Soulboy420/BP_flappyBird/hardware/redesign/doc/quellen.md

# Herstellerquellen und Pinprüfung

Recherche 05.–06.09.2026. Maßgeblich sind die verlinkten Originalunterlagen, nicht Händler-Kurztexte. „S.“ bezeichnet die im PDF gedruckte Seite, soweit vorhanden; sonst die PDF-Seite. Produktseiten ohne Revision sind mit Abrufdatum dokumentiert. Lokale PDFs unter `quellen/` sind ergänzende Arbeitskopien; deren Fehlen bedeutet nicht, dass eine unten verlinkte Quelle offline mitgeliefert wird. Typische Kurven werden nicht als garantierte Grenzwerte ausgegeben.

## Aktive Bauteile und Architektur

| Bauteil / Quelle | Revision / Fundstelle | Geprüfte Aussage und Umsetzung |
|---|---|---|
| [Espressif ESP32-C3-WROOM-02](https://www.espressif.com/sites/default/files/documentation/esp32-c3-wroom-02_datasheet_en.pdf) | v1.7; Pin Definitions, Strapping Pins, Electrical Characteristics, Module Dimensions | U1.1 Versorgung, .2 EN, .3–.8 GPIO4–9, .9 GND, .10 GPIO10, .11/.12 GPIO20/21, .13/.14 GPIO18/19, .15–.18 GPIO3–0, .19 EP/GND. 3,0…3,6 V, Straps 2/8/9, Modulgeometrie. |
| [ESP32-C3 SoC](https://documentation.espressif.com/esp32-c3_datasheet_en.html) | v2.4; §2.4, §3.1/3.2 | GPIO21 ist ROM-UART-TX; deshalb nur LED an diesem Pin. GPIO2 steuert EN2 invertiert über Q7. GPIO3 ist RTC-Wake-Eingang. |
| [Espressif Hardware Design Guidelines](https://documentation.espressif.com/esp-hardware-design-guidelines/en/latest/esp32c3/index.html) | v1.8; Schematic Checklist / PCB Layout Design | USB-Serienwiderstände, 90-Ω-Ziel und Antennenfreiraum. Tatsächlicher Fertigeraufbau bleibt Freigabepunkt. |
| [TI BQ24074](https://www.ti.com/lit/ds/symlink/bq24074.pdf) | SLUS810N, Okt. 2021; §7, §8.5, §9, Layout/Package | U2: 1 TS, 2/3 BAT, 4 CE, 5 EN2, 6 EN1, 7 PGOOD, 8 VSS, 9 CHG, 10/11 OUT, 12 ILIM, 13 IN, 14 TMR, 15 ITERM, 16 ISET, 17 EP. RGT 3×3 mm, Pitch 0,5 mm, EP 1,6×1,6 mm. KISET 797/890/975; VREG bis 4,23 V; IN absolut 28 V. Eigenständiger Lastpfad verhindert verfälschten Ladeabschluss. TS-Grenzen rechtfertigen keine garantierte 0…45-°C-Freigabe. |
| [Torex XC6220](https://product.torexsemi.com/system/files/series/xc6220.pdf) / [Produktserie](https://product.torexsemi.com/en/series/xc6220) | ETR03041-016b; S.3–6,11, Package Information | **PR/SOT-89-5: 1 CE, 2 GND, 3 NC, 4 VIN, 5 VOUT.** Lokales Symbol explizit umgepinnt. PS-Ruhestrom 8 µA typisch/18 µA max unter Testbedingungen; HS 50/108 µA. 10-µF-Referenzbeschaltung. Kein aus typischem Dropout abgeleiteter garantierter Mindest-Akkustand. |
| [TI TPS22919](https://www.ti.com/lit/ds/symlink/tps22919.pdf) | SLVSEN5B, Mai 2019; Pin Configuration, Electrical Characteristics, QOD | U4 DCK: 1 IN, 2 GND, 3 ON, 4 NC, 5 QOD, 6 OUT. OLED und U5 gemeinsam abschaltbar. Ausschaltstrom bis 800 nA über spezifizierten Temperaturbereich. |
| [Nexperia 74LVC125A](https://assets.nexperia.com/documents/data-sheet/74LVC125A.pdf) / [Bestellcodes](https://www.nexperia.com/products/analog-logic-ics/logic/buffers-inverters-transceivers/buffers/serie/74lvc125a/) | Rev.12, 02.05.2025; S.3 Pinning, S.4–6 Limits/Characteristics, Package SOT108-1 | U5 **74LVC125AD,118**, SO14: OE 1/4/10/13, A 2/5/9/12, Y 3/6/8/11, GND 7, VCC 14. IOFF ausdrücklich für ausgeschaltete Versorgung spezifiziert; max. 10 µA je Pin bis 85 °C. Vier 220-Ω-Serienwiderstände begrenzen Kurzschlussstrom. Kein ungeprüfter Herstellerersatz. |
| [TI TPD2E2U06](https://www.ti.com/lit/ds/symlink/tpd2e2u06.pdf) | Rev.C; Pin Configuration / Electrical Characteristics / DCK | D2…D9, **SC70-3: 1 IO1, 2 IO2, 3 GND**, kein VCC-Pin. 5,5-V-Standoff, geringe Kapazität. Die angegebenen ESD-Pegel gelten für das Bauteil unter dessen Prüfbedingungen. |
| [Diodes DMP2035U](https://www.diodes.com/datasheet/download/DMP2035U.pdf) | DS31830 Rev.11-2, Juni 2025; S.1–3 | Q1 SOT23: 1 G, 2 S, 3 D. 20 V VDS, ±10 V VGS, max. 45 mΩ bei −2,5 V. Source am BQ-BAT-Knoten, Drain am Pack. |
| [Diodes BSS84](https://www.diodes.com/datasheet/download/BSS84.pdf) | DS30149 Rev.27-2, Mai 2026; S.1–3 | Q2/Q4: 1 G, 2 S, 3 D. P-Kanal, 50 V VDS, ±20 V VGS. Einsatz als Detektor bzw. Kleinstrom-Messzweig, nicht als Hauptleistungs-FET. |
| [Diodes 2N7002](https://www.diodes.com/datasheet/download/2N7002.pdf) | Datenblatt am 05.09.2026; S.1–3 / Pin Assignment, Electrical Characteristics | Q3/Q5/Q7: 1 G, 2 S, 3 D. Nur kleine Pullup-/Gate-Ströme. Kein aus dem Namen abgeleiteter 3,3-V-Leistungsbetrieb. |
| [Diodes DMN2056U](https://www.diodes.com/datasheet/download/DMN2056U.pdf) | DS38480 Rev.2-2, Juli 2021; S.1–3 | Q6: 1 G, 2 S, 3 D; bei 2,5 V spezifizierter Logic-Level-FET; 45 mΩ max., VDS 20 V, VGS ±8 V. Piezo über MOSFET statt direkt am GPIO. |
| [Diodes BAV19W–BAV21W](https://www.diodes.com/datasheet/download/BAV19W-BAV21W.pdf) / [BAV19W](https://www.diodes.com/part/view/BAV19W) | Datenblatt am 05.09.2026; Pin Assignment / Package / Characteristics | D12 BAV19W-7-F, SOD123. Band = Kathode = PCB-Pad 1 an PIEZO_P; Pad 2 Anode an PIEZO_N. Rückschlagklemme für kapazitive Last. |
| [ADI AN-171](https://www.analog.com/en/resources/app-notes/an-171.html) | Reverse Voltage Protection for Battery Chargers, insbesondere Abb.7 | Zwei-PMOS-Verpolerkennung; mögliche Verriegelung beim Akkuwechsel mit bereits aktivem Ladeeingang. R6 bleibt DNP, Akku-vor-USB als dokumentierte Einschränkung. Keine ungemessene Hot-Swap-Garantie. |

## Passive Bauteile, Schutz und Mechanik

| Bauteil / Quelle | Fundstelle | Prüfung / Entscheidung |
|---|---|---|
| [Littelfuse 466 Sicherung](https://www.littelfuse.com/assetdocs/fuse-466-datasheet?assetguid=dbe9bcd7-6072-4adf-bf5b-d33e52a6b90f) | GD 06/21/23; S.1 Electrical Characteristics, S.2 Derating, S.3 Dimensions/Ordering | **0466001.NRHF**, 1 A, 1206, 63 V. 3,175×1,524 mm; symmetrische Pads 1/2. 75 mΩ typ., 2× Nennstrom: max.5 s; 3×: max.0,2 s. Nicht mit der kleineren 467-Familie verwechseln. |
| [Littelfuse SMBJ](https://www.littelfuse.com/~/media/electronics/datasheets/tvs_diodes/littelfuse_tvs_diode_smbj_datasheet.pdf.pdf) | 2020-Fassung; Electrical Characteristics, Case Dimensions, Polarity | SMBJ6.0A unidirektional, SMB. 6,0-V-Standoff, 10,3 V Klemmung bei 58,3 A im spezifizierten Puls. Kathodenband an VBUS/Pad 1. Der neuere indizierte Herstellerlink lieferte beim Direktabruf 404; kein behaupteter Vergleich einer nicht lesbaren neuen PDF-Fassung. |
| [TDK 22 µF / 16 V](https://product.tdk.com/en/search/capacitor/ceramic/mlcc/info?part_no=C3216X5R1C226M160AB) / [Charakterisierungsblatt](https://product.tdk.com/en/system/files/dam/doc/product/capacitor/ceramic/mlcc/charasheet/c3216x5r1c226m160ab.pdf) | Produktseite „Production“, Abruf 05.09.2026; Charakterisierungsblatt 03.01.2016, 1 Seite | C3…C11: 1206, 3,2×1,6 mm, 1,6 mm Höhe, ±20 %, X5R, IR ≥4 MΩ. DC-Bias-Kurve vorhanden; Bildabruf nicht erfolgreich, deshalb keine erfundene Kurvenablesung. Kapazitätsfreigabe explizit offen. |
| [TDK 100 nF](https://product.tdk.com/en/search/capacitor/ceramic/mlcc/info?part_no=C2012X7R1H104K085AA) | Produktseite, Abruf 05.09.2026 | C2012X7R1H104K085AA, 0805, 50 V, X7R. Nichtpolar, Pads 1/2 austauschbar. |
| [TDK 1 µF](https://product.tdk.com/en/search/capacitor/ceramic/mlcc/info?part_no=C2012X7R1E105K125AB) | Produktseite, Abruf 05.09.2026 | C2012X7R1E105K125AB, 0805, 25 V, X7R, ±10 %. |
| [KEMET 18 pF](https://search.kemet.com/download/specsheet/C0805C180J5GACTU) | S.1, Abruf 05.09.2026 | C17/C18 DNP: C0805C180J5GACTU, 0805, 50 V, C0G, ±5 %. |
| [Panasonic Null-Ohm](https://industrial.panasonic.com/ww/products/pt/general-purpose-chip-resistors/models/ERJ6GEY0R00V) / [ERJ6ENF-Familienbeispiel](https://industrial.panasonic.com/jp/products/pt/general-purpose-chip-resistors/models/ERJ6ENF28R0V) | Produktdaten / Dimensions / Rating, Abruf 05.09.2026 | ERJ-6GEY0R00V für 0 Ω; ERJ-6ENF-Wertcodes gemäß BOM für 1 %, 0805, 0,125 W. Unpolar. R36 nahe seiner Belastungsgrenze bei Dauerkurzschluss; Temperatur-Derating beachten. |
| [GCT USB4105 Zeichnung](https://gct.co/files/drawings/usb4105.pdf) / [Spezifikation](https://gct.co/files/specs/usb4105-spec.pdf) | Zeichnung Pin Assignment; Spec Rev.A3, 27.02.2023 | USB4105-GF-A. A1/B12 etc. Masse, A4/B9 etc. VBUS, A5 CC1/B5 CC2, A6/B6 D+, A7/B7 D−, SBU NC. Doppelte Signalkontakte verbunden; mechanische Schirmanschlüsse auf GND. |
| [JST PH](https://www.jst-mfg.com/product/pdf/eng/ePH.pdf) | PCB Layout / Header / Ordering, Abruf 05.09.2026 | B2B-PH-K-S(LF)(SN), 2,00-mm-Raster. Physische Pin-1-Ansicht geprüft; die Zuordnung zu Akku+ bzw. NTC legt dieser Entwurf fest. Ein PH-Gehäuse garantiert keine fremde Kabelpolung. |
| [JST XH](https://www.jst-mfg.com/product/pdf/eng/eXH.pdf) | S.2 Leiterplattenansicht, S.5 Top Entry Header, Abruf 06.09.2026 | B8B-XH-A(LF)(SN): 2,50-mm-Raster, Pinspanne 17,5 mm, Körperbreite 22,4 mm. B2B-XH-A für J4/J5. Pad1 ist markiert; 1:1-Abgleich mit Gegensteckern bleibt nötig. |
| [C&K OS Series](https://www.littelfuse.com/assetdocs/littelfuse-ck-slide-os-series-datasheet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) | CM 06/16/25; S.1 Kontaktmaterial, S.3 OS102 | OS102011MS2QN1: SPDT, Pin2 gemeinsam, 1–2/2–3, nicht kurzschließend; drei elektrische und zwei Befestigungsbohrungen. Keine bestätigte Mindestlast für wenige µA; Schaltzuverlässigkeit am Prototyp prüfen. |
| [Semitec AT](https://www.semitec-global.com/uploads/2022/01/NTC_thermistors_Circuit_129M.pdf) / [Serie](https://www.semitec-global.com/products/thermistor_at/) | 103AT-2-Zeile, R/T und Thermal Time Constant | Externes NTC-Teil 10 kΩ ±1 %, B=3435 K ±1 %, ca.15 s thermische Zeitkonstante. Nicht polar; thermische Befestigung am Pack ist Teil der Qualifikation. |
| [Kingbright APT2012EC](https://www.kingbrightusa.com/images/catalog/spec/apt2012ec.pdf) / [APT2012SGC](https://www.kingbrightusa.com/images/catalog/spec/apt2012sgc.pdf) | EC Ver.13A 2021 / SGC 2025; Package Dimensions / Polarity / Electrical | D10 rot, D11 grün, 0805. Kathode Pad1, Anode Pad2. Serienwiderstand 3,3 kΩ; Lichtstärke bei kleinem Strom messen. |

## Leiterbahn-Vorabschätzung

[TI SNVA766, April 2017, S.16, Gleichung 3](https://www.ti.com.cn/cn/lit/pdf/snva766) dokumentiert die verwendete IPC-2221-Näherung für Außenlagen. Sie liefert eine rechnerische Eigenerwärmung, keine validierte Gehäusetemperatur. Die Annahmen und aus dem PCB ausgelesenen VBAT-Leiterlängen stehen in `designentscheidungen.md`.

## Quellen zum Ausgangsentwurf

- [Microchip MCP73831/2, DS20001984G](https://ww1.microchip.com/downloads/en/DeviceDoc/20001984g.pdf), Charge Termination / Typical Application: Systemlast am BAT-Knoten beeinflusst den Abschluss.
- [Microchip AN1149](https://ww1.microchip.com/downloads/en/Appnotes/01149c.pdf), Load Sharing: zusätzlicher Systempfad erforderlich, wenn Laden und Last unabhängig behandelt werden sollen.
- [Diodes AP2112, DS39724 Rev.2-2, Juni 2017](https://www.diodes.com/datasheet/download/AP2112.pdf), S.8: Ruhestrom typ.55/max.80 µA, Ausschaltstrom typ.0,01/max.1 µA. Kein 5-µA-Gesamtbudget mit dauerhaft aktivem Regler.

## Reichweite des Pin-Nachweises

`output/pinmapping.csv` listet jedes physische nummerierte Pad mit Herstellerteilenummer, Symbolpin und tatsächlichem Netz. `verification/consistency.json` gleicht diese Zuordnung unabhängig zwischen nativer XML-Netzliste und gespeichertem PCB ab. Identische Mehrfachpads (USB-Schirm, EP) müssen dasselbe Netz führen. NC-Pins sind ausdrücklich unverbunden; Bohrungen besitzen keine elektrischen Pins. Unpolare R/C/Sicherungen sind symmetrisch. LEDs, Dioden, FETs und ICs wurden anhand der oben genannten Pin-/Gehäusezeichnungen geprüft. Für freie Testpads ist keine Keystone-Montage vorgesehen; der BOM-Hinweis ist kein Bestückungsauftrag.

Die lokalen KiCad-Footprints enthalten die verbindlichen Lötflächen. U2 nutzt einen geometrisch passenden generischen WQFN-3D-Körper; U3 einen vereinfachten SOT-89-5-Hüllkörper. Diese beiden Visualisierungsmodelle ersetzen keine Herstellerzeichnung und sind keine mechanische Freigabe.
