Soulboy420/BP_flappyBird/hardware/redesign/output/platine-3d.png

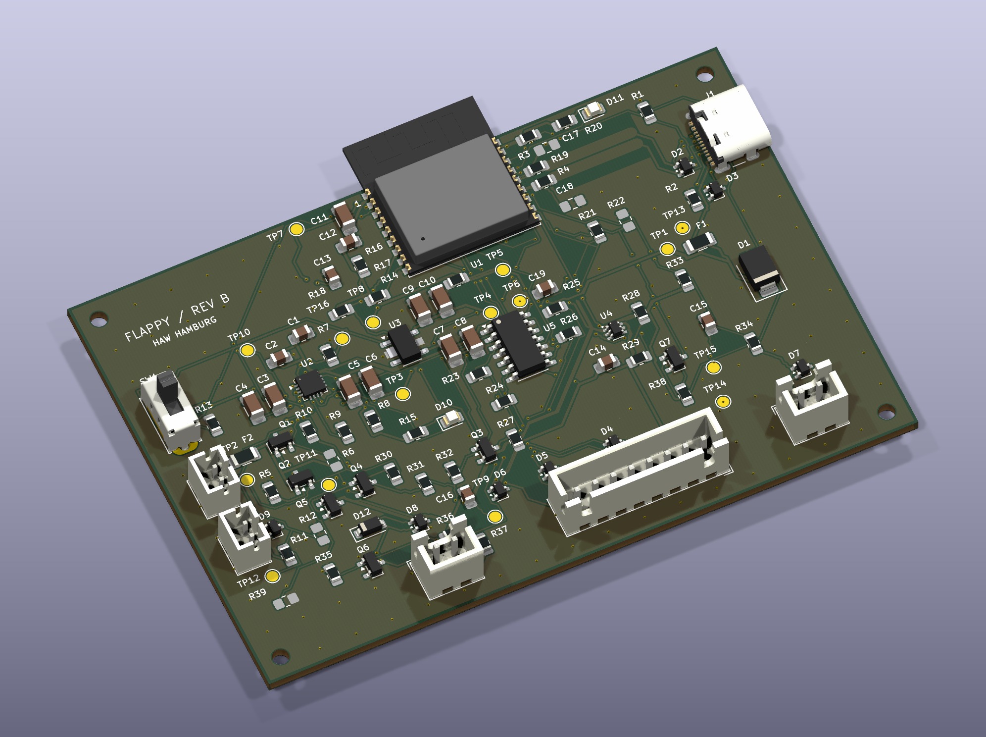
hardware/redesign/output/platine-3d.png
