Soulboy420/BP_flappyBird/hardware/redesign/verification/pdf-render/schaltplan-5.png

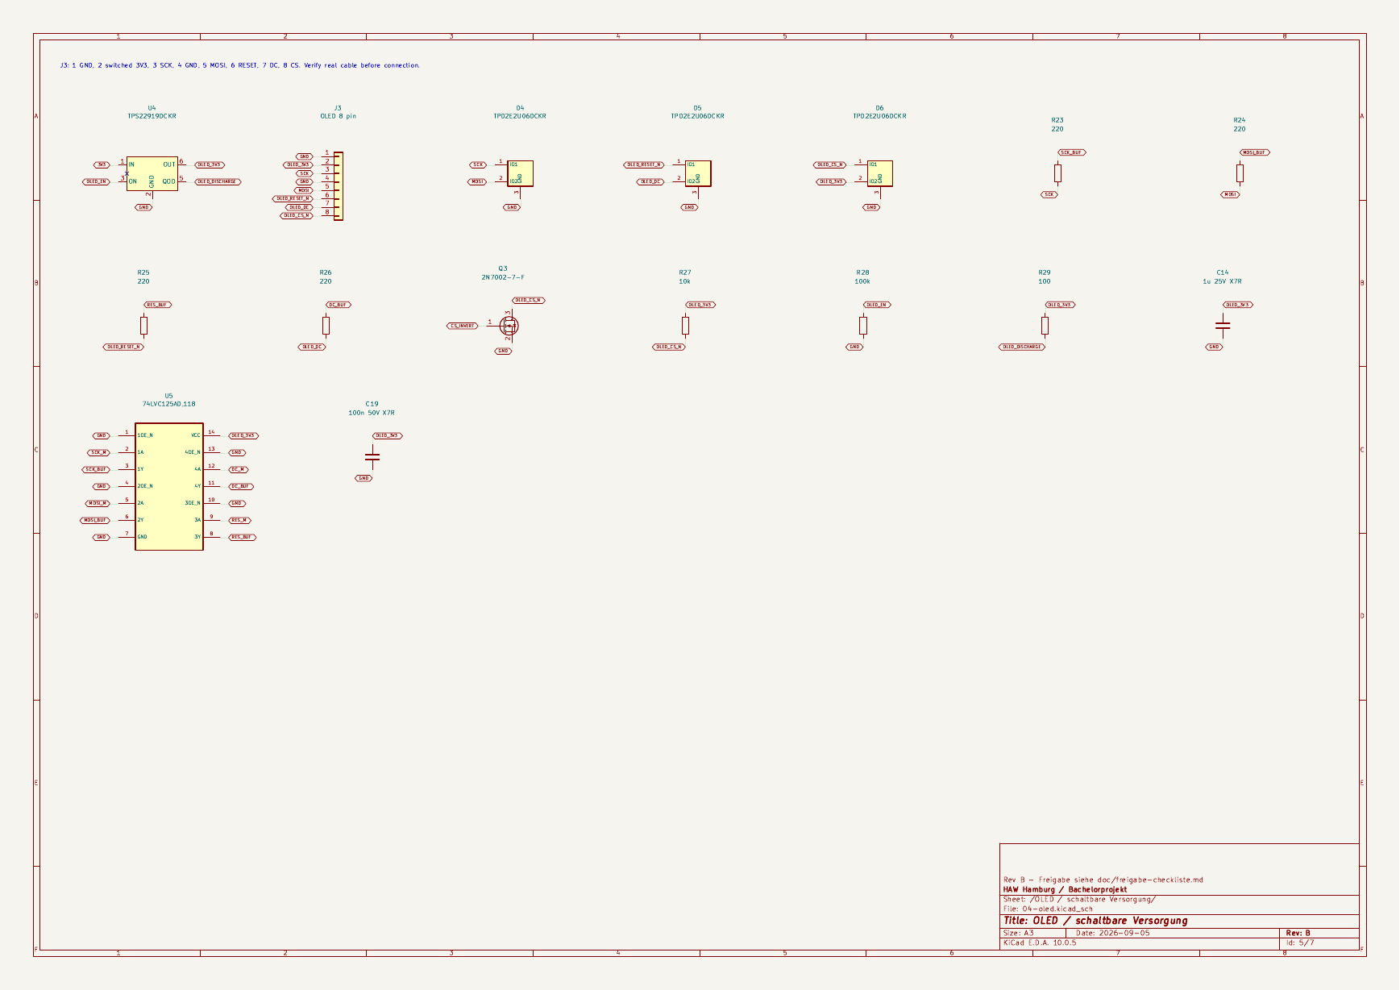
hardware/redesign/verification/pdf-render/schaltplan-5.png
