Soulboy420/BP_flappyBird/hardware/redesign/verification/pdf-render/schaltplan-6.png

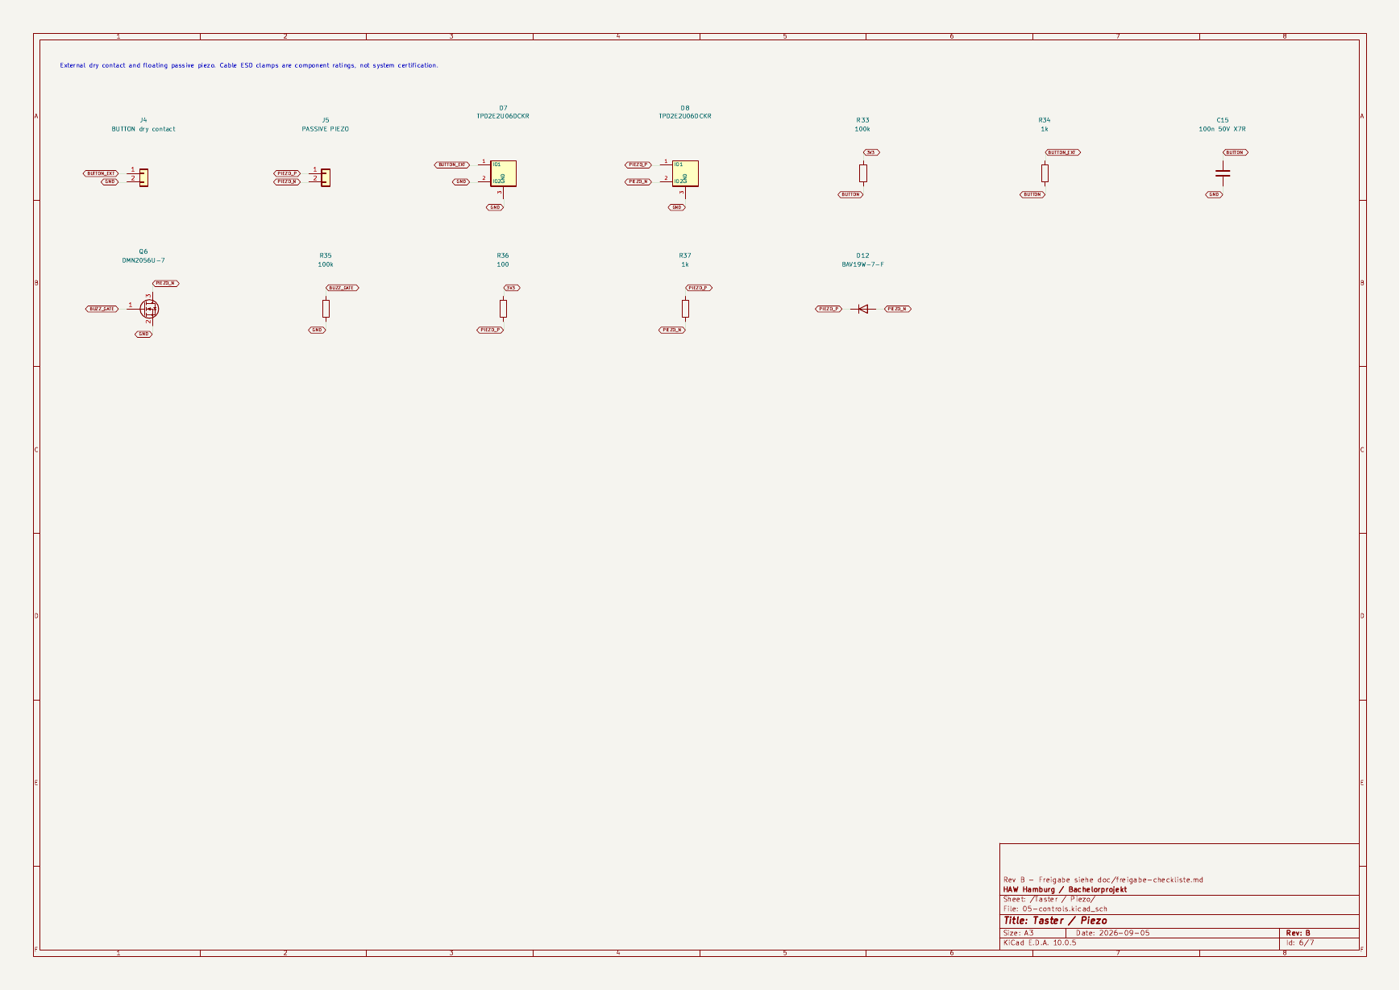
hardware/redesign/verification/pdf-render/schaltplan-6.png
