Soulboy420/BP_flappyBird/hardware/gen/routes.py

# -*- coding: utf-8 -*-
"""Automatisch erzeugt von autoroute.py - nicht von Hand aendern."""
TRACKS = [('GND', 'F.Cu', 0.4, (22.65, 20.0), (22.6, 20.0)), ('GND', 'F.Cu', 0.4, (22.6, 20.0), (21.0, 20.0)), ('GND', 'F.Cu', 0.4, (42.65, 10.0), (42.6, 10.0)), ('GND', 'F.Cu', 0.4, (42.6, 10.0), (41.0, 10.0)), ('GND', 'F.Cu', 0.4, (73.15, 51.5), (73.2, 51.5)), ('GND', 'F.Cu', 0.4, (73.2, 51.5), (73.2, 51.6)), ('GND', 'F.Cu', 0.4, (73.2, 51.6), (71.6, 51.6)), ('VBAT', 'F.Cu', 0.5, (42.6, 11.0), (44.6, 13.0)), ('VBAT', 'F.Cu', 0.5, (44.6, 13.0), (52.0, 13.0)), ('VBAT', 'F.Cu', 0.5, (52.0, 13.0), (56.0, 13.0)), ('VBAT', 'F.Cu', 0.5, (56.0, 13.0), (56.8, 13.8)), ('VBAT', 'F.Cu', 0.5, (56.8, 13.8), (57.4, 13.8)), ('VBAT', 'F.Cu', 0.5, (57.4, 13.8), (57.6, 14.0)), ('VBAT', 'F.Cu', 0.5, (57.6, 14.0), (62.0, 14.0)), ('VBAT', 'F.Cu', 0.5, (62.0, 14.0), (66.4, 14.0)), ('VBAT', 'F.Cu', 0.5, (66.4, 14.0), (69.0, 11.4)), ('VBAT', 'F.Cu', 0.5, (69.0, 11.4), (69.0, 8.0)), ('VBAT', 'F.Cu', 0.5, (66.6, 13.8), (72.8, 20.0)), ('VBAT', 'F.Cu', 0.5, (72.8, 20.0), (73.4, 20.0)), ('VBAT', 'F.Cu', 0.5, (73.4, 20.0), (74.0, 20.6)), ('VBAT', 'F.Cu', 0.5, (74.0, 20.6), (74.0, 22.0)), ('VBAT', 'F.Cu', 0.5, (74.0, 22.0), (73.4, 22.6)), ('VBAT', 'F.Cu', 0.5, (73.4, 22.6), (73.4, 24.0)), ('VBAT', 'F.Cu', 0.5, (73.4, 24.0), (73.2, 24.2)), ('VBAT', 'F.Cu', 0.5, (73.2, 24.2), (73.2, 50.6)), ('VBAT', 'F.Cu', 0.5, (73.2, 50.4), (71.6, 50.4)), ('VBAT', 'F.Cu', 0.5, (71.6, 50.4), (71.4, 50.6)), ('VBAT', 'F.Cu', 0.5, (71.4, 50.6), (71.0, 50.6)), ('VBAT', 'F.Cu', 0.5, (71.0, 50.6), (69.0, 52.6)), ('VBAT', 'F.Cu', 0.5, (69.0, 52.6), (69.0, 57.6)), ('VBAT', 'F.Cu', 0.5, (44.6, 13.0), (42.4, 15.2)), ('VBAT', 'F.Cu', 0.5, (42.4, 15.2), (42.4, 16.4)), ('VBAT', 'F.Cu', 0.5, (42.4, 16.4), (35.0, 23.8)), ('VBAT', 'F.Cu', 0.5, (35.0, 23.8), (35.0, 33.0)), ('BATT_P', 'F.Cu', 0.6, (67.0, 8.0), (67.6, 7.4)), ('BATT_P', 'F.Cu', 0.6, (67.6, 7.4), (67.6, 6.6)), ('BATT_P', 'F.Cu', 0.6, (67.6, 6.6), (70.4, 6.6)), ('BATT_P', 'F.Cu', 0.6, (70.4, 6.6), (71.8, 8.0)), ('BATT_P', 'F.Cu', 0.6, (71.8, 8.0), (76.0, 8.0)), ('USB_DM_CON', 'F.Cu', 0.3, (13.6, 13.0), (14.8, 14.2)), ('USB_DM_CON', 'F.Cu', 0.3, (14.8, 14.2), (15.0, 14.2)), ('USB_DM_CON', 'F.Cu', 0.3, (15.0, 14.2), (17.8, 17.0)), ('USB_DM_CON', 'F.Cu', 0.3, (17.8, 17.0), (17.8, 17.8)), ('USB_DM_CON', 'F.Cu', 0.3, (17.8, 17.8), (19.0, 19.0)), ('USB_DM_CON', 'F.Cu', 0.3, (19.0, 19.0), (22.6, 19.0)), ('VBUS', 'F.Cu', 0.4, (13.6, 8.0), (14.6, 7.0)), ('VBUS', 'F.Cu', 0.4, (14.6, 7.0), (32.0, 7.0)), ('VBUS', 'F.Cu', 0.4, (32.0, 7.0), (36.0, 7.0)), ('VBUS', 'F.Cu', 0.4, (30.6, 7.0), (30.6, 10.2)), ('VBUS', 'F.Cu', 0.4, (30.6, 10.2), (32.0, 11.6)), ('VBUS', 'F.Cu', 0.4, (32.0, 11.6), (32.0, 12.4)), ('VBUS', 'F.Cu', 0.4, (32.0, 12.4), (26.8, 17.6)), ('VBUS', 'F.Cu', 0.4, (26.8, 17.6), (26.8, 20.0)), ('VBUS', 'F.Cu', 0.4, (26.8, 20.0), (25.4, 20.0)), ('VBUS', 'F.Cu', 0.4, (25.4, 20.0), (24.0, 20.0)), ('VBUS', 'F.Cu', 0.4, (24.0, 20.0), (24.0, 22.0)), ('VBUS', 'F.Cu', 0.4, (24.0, 22.0), (23.4, 22.6)), ('VBUS', 'F.Cu', 0.4, (23.4, 22.6), (19.8, 22.6)), ('VBUS', 'F.Cu', 0.4, (19.8, 22.6), (19.0, 23.4)), ('VBUS', 'F.Cu', 0.4, (19.0, 23.4), (19.0, 24.0)), ('VBUS', 'F.Cu', 0.4, (36.0, 7.0), (37.4, 7.0)), ('VBUS', 'F.Cu', 0.4, (37.4, 7.0), (38.4, 8.0)), ('VBUS', 'F.Cu', 0.4, (38.4, 8.0), (44.0, 8.0)), ('VBUS', 'F.Cu', 0.4, (44.0, 8.0), (44.0, 10.0)), ('VBUS', 'F.Cu', 0.4, (44.0, 10.0), (45.0, 11.0)), ('VBUS', 'F.Cu', 0.4, (45.0, 11.0), (45.4, 11.0)), ('VBUS', 'F.Cu', 0.4, (45.4, 11.0), (46.4, 10.0)), ('VBUS', 'F.Cu', 0.4, (46.4, 10.0), (46.8, 10.0)), ('VBUS', 'F.Cu', 0.4, (46.8, 10.0), (48.8, 8.0)), ('VBUS', 'F.Cu', 0.4, (48.8, 8.0), (51.0, 8.0)), ('USB_DP', 'F.Cu', 0.3, (31.8, 46.8), (30.4, 46.8)), ('USB_DP', 'F.Cu', 0.3, (30.4, 46.8), (30.0, 46.4)), ('USB_DP', 'F.Cu', 0.3, (30.0, 46.4), (29.8, 46.4)), ('USB_DP', 'F.Cu', 0.3, (29.8, 46.4), (29.6, 46.2)), ('USB_DP', 'F.Cu', 0.3, (29.6, 46.2), (29.6, 36.0)), ('USB_DP', 'F.Cu', 0.3, (29.6, 36.0), (28.2, 34.6)), ('USB_DP', 'F.Cu', 0.3, (28.2, 34.6), (28.2, 28.6)), ('USB_DP', 'F.Cu', 0.3, (28.2, 28.6), (27.2, 27.6)), ('USB_DP', 'F.Cu', 0.3, (27.2, 27.6), (27.2, 22.6)), ('USB_DP', 'F.Cu', 0.3, (27.2, 22.6), (25.6, 21.0)), ('USB_DP', 'F.Cu', 0.3, (25.6, 21.0), (25.4, 21.0)), ('+3V3_MCU', 'F.Cu', 0.5, (50.2, 52.8), (50.4, 52.6)), ('+3V3_MCU', 'F.Cu', 0.5, (50.4, 52.6), (53.0, 52.6)), ('+3V3_MCU', 'F.Cu', 0.5, (53.0, 52.6), (61.0, 52.6)), ('+3V3_MCU', 'F.Cu', 0.5, (61.0, 52.6), (65.0, 52.6)), ('+3V3_MCU', 'F.Cu', 0.5, (65.0, 52.6), (65.6, 53.2)), ('+3V3_MCU', 'F.Cu', 0.5, (65.6, 53.2), (65.6, 54.0)), ('+3V3_MCU', 'F.Cu', 0.5, (65.6, 54.0), (66.0, 54.4)), ('+3V3_MCU', 'F.Cu', 0.5, (66.0, 54.4), (66.0, 57.2)), ('+3V3_MCU', 'F.Cu', 0.5, (58.4, 52.6), (58.4, 42.4)), ('+3V3_MCU', 'F.Cu', 0.5, (58.4, 42.4), (57.0, 41.0)), ('+3V3_MCU', 'F.Cu', 0.5, (57.0, 41.0), (57.0, 40.4)), ('+3V3_MCU', 'F.Cu', 0.5, (65.0, 52.6), (65.6, 52.0)), ('+3V3_MCU', 'F.Cu', 0.5, (65.6, 52.0), (65.6, 51.2)), ('+3V3_MCU', 'F.Cu', 0.5, (65.6, 51.2), (69.0, 47.8)), ('+3V3_MCU', 'F.Cu', 0.5, (69.0, 47.8), (69.0, 44.0)), ('+3V3_MCU', 'F.Cu', 0.5, (57.0, 40.4), (56.4, 39.8)), ('+3V3_MCU', 'F.Cu', 0.5, (56.4, 39.8), (56.4, 39.0)), ('+3V3_MCU', 'F.Cu', 0.5, (56.4, 39.0), (55.0, 37.6)), ('+3V3_MCU', 'F.Cu', 0.5, (55.0, 37.6), (55.0, 36.6)), ('+3V3_MCU', 'F.Cu', 0.5, (55.0, 36.6), (31.4, 36.6)), ('+3V3_MCU', 'F.Cu', 0.5, (31.4, 36.6), (29.8, 35.0)), ('+3V3_MCU', 'B.Cu', 0.5, (29.8, 35.0), (28.6, 36.2)), ('+3V3_MCU', 'F.Cu', 0.5, (28.6, 36.2), (26.2, 38.6)), ('+3V3_MCU', 'F.Cu', 0.5, (26.2, 38.6), (21.6, 38.6)), ('+3V3_MCU', 'F.Cu', 0.5, (21.6, 38.6), (21.0, 39.2)), ('+3V3_MCU', 'F.Cu', 0.5, (21.0, 39.2), (21.0, 40.0)), ('+3V3_MCU', 'F.Cu', 0.5, (24.8, 38.6), (24.8, 36.0)), ('+3V3_MCU', 'F.Cu', 0.5, (24.8, 36.0), (23.4, 36.0)), ('+3V3_MCU', 'F.Cu', 0.5, (21.0, 40.0), (13.6, 47.4)), ('+3V3_MCU', 'F.Cu', 0.5, (13.6, 47.4), (11.4, 47.4)), ('+3V3_MCU', 'F.Cu', 0.5, (11.4, 47.4), (10.2, 48.6)), ('+3V3_MCU', 'F.Cu', 0.5, (10.2, 48.6), (9.6, 48.6)), ('+3V3_MCU', 'F.Cu', 0.5, (9.6, 48.6), (9.0, 49.2)), ('+3V3_MCU', 'F.Cu', 0.5, (9.0, 49.2), (9.0, 50.0)), ('USB_DM', 'F.Cu', 0.3, (31.8, 45.4), (30.8, 45.4)), ('USB_DM', 'F.Cu', 0.3, (30.8, 45.4), (30.6, 45.6)), ('USB_DM', 'B.Cu', 0.3, (30.6, 45.6), (29.2, 47.0)), ('USB_DM', 'F.Cu', 0.3, (29.2, 47.0), (25.8, 47.0)), ('USB_DM', 'F.Cu', 0.3, (25.8, 47.0), (25.4, 47.4)), ('USB_DM', 'F.Cu', 0.3, (25.4, 47.4), (16.2, 47.4)), ('USB_DM', 'F.Cu', 0.3, (16.2, 47.4), (12.2, 51.4)), ('USB_DM', 'F.Cu', 0.3, (12.2, 51.4), (7.8, 51.4)), ('USB_DM', 'F.Cu', 0.3, (7.8, 51.4), (7.8, 48.6)), ('USB_DM', 'F.Cu', 0.3, (7.8, 48.6), (9.0, 47.4)), ('USB_DM', 'F.Cu', 0.3, (9.0, 47.4), (9.4, 47.4)), ('USB_DM', 'F.Cu', 0.3, (9.4, 47.4), (13.8, 43.0)), ('USB_DM', 'F.Cu', 0.3, (13.8, 43.0), (13.8, 38.6)), ('USB_DM', 'F.Cu', 0.3, (13.8, 38.6), (17.8, 34.6)), ('USB_DM', 'F.Cu', 0.3, (17.8, 34.6), (17.8, 22.6)), ('USB_DM', 'F.Cu', 0.3, (17.8, 22.6), (18.0, 22.4)), ('USB_DM', 'F.Cu', 0.3, (18.0, 22.4), (18.0, 19.2)), ('USB_DM', 'B.Cu', 0.3, (18.0, 19.2), (19.2, 18.0)), ('USB_DM', 'F.Cu', 0.3, (19.2, 18.0), (19.4, 18.2)), ('USB_DM', 'F.Cu', 0.3, (19.4, 18.2), (24.0, 18.2)), ('USB_DM', 'F.Cu', 0.3, (24.0, 18.2), (24.8, 19.0)), ('USB_DM', 'F.Cu', 0.3, (24.8, 19.0), (25.4, 19.0)), ('USB_DP_CON', 'F.Cu', 0.3, (13.6, 15.6), (14.6, 16.6)), ('USB_DP_CON', 'F.Cu', 0.3, (14.6, 16.6), (15.0, 16.6)), ('USB_DP_CON', 'F.Cu', 0.3, (15.0, 16.6), (17.0, 18.6)), ('USB_DP_CON', 'F.Cu', 0.3, (17.0, 18.6), (17.0, 20.2)), ('USB_DP_CON', 'B.Cu', 0.3, (17.0, 20.2), (19.0, 20.2)), ('USB_DP_CON', 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
 30.2)), ('LDO_EN', 'F.Cu', 0.25, (78.6, 30.2), (84.8, 36.4)), ('LDO_EN', 'F.Cu', 0.25, (84.8, 36.4), (85.0, 36.4)), ('LDO_EN', 'F.Cu', 0.25, (85.0, 36.4), (85.6, 37.0)), ('LDO_EN', 'F.Cu', 0.25, (85.6, 37.0), (85.6, 57.4)), ('LDO_EN', 'F.Cu', 0.25, (85.6, 57.4), (82.4, 57.4)), ('LDO_EN', 'F.Cu', 0.25, (82.4, 57.4), (82.2, 57.2)), ('LDO_EN', 'F.Cu', 0.25, (82.2, 57.2), (78.2, 57.2)), ('LDO_EN', 'F.Cu', 0.25, (78.2, 57.2), (77.6, 56.6)), ('LDO_EN', 'B.Cu', 0.25, (77.6, 56.6), (76.2, 55.2)), ('LDO_EN', 'F.Cu', 0.25, (76.2, 55.2), (74.6, 53.6)), ('LDO_EN', 'F.Cu', 0.25, (74.6, 53.6), (74.4, 53.6)), ('LDO_EN', 'F.Cu', 0.25, (74.4, 53.6), (73.2, 52.4)), ('VBAT_SENSE', 'F.Cu', 0.25, (31.8, 52.8), (29.8, 52.8)), ('VBAT_SENSE', 'F.Cu', 0.25, (29.8, 52.8), (29.4, 53.2)), ('VBAT_SENSE', 'F.Cu', 0.25, (29.4, 53.2), (25.6, 53.2)), ('VBAT_SENSE', 'F.Cu', 0.25, (25.6, 53.2), (25.4, 53.4)), ('VBAT_SENSE', 'F.Cu', 0.25, (25.4, 53.4), (24.0, 53.4)), ('VBAT_SENSE', 'F.Cu', 0.25, (24.0, 53.4), (20.6, 56.8)), ('VBAT_SENSE', 'F.Cu', 0.25, (20.6, 56.8), (19.6, 56.8)), ('VBAT_SENSE', 'F.Cu', 0.25, (19.6, 56.8), (19.0, 57.4)), ('VBAT_SENSE', 'F.Cu', 0.25, (19.0, 57.4), (11.0, 57.4)), ('VBAT_SENSE', 'F.Cu', 0.25, (11.0, 57.4), (10.8, 57.2)), ('VBAT_SENSE', 'F.Cu', 0.25, (10.8, 57.2), (2.2, 57.2)), ('VBAT_SENSE', 'F.Cu', 0.25, (2.2, 57.2), (2.0, 57.0)), ('VBAT_SENSE', 'F.Cu', 0.25, (2.0, 57.0), (2.0, 53.0)), ('VBAT_SENSE', 'F.Cu', 0.25, (2.0, 53.0), (5.4, 49.6)), ('VBAT_SENSE', 'F.Cu', 0.25, (5.4, 49.6), (5.4, 43.8)), ('VBAT_SENSE', 'F.Cu', 0.25, (5.4, 43.8), (7.2, 42.0)), ('VBAT_SENSE', 'F.Cu', 0.25, (7.2, 42.0), (7.2, 38.4)), ('VBAT_SENSE', 'F.Cu', 0.25, (7.2, 38.4), (10.6, 35.0)), ('VBAT_SENSE', 'F.Cu', 0.25, (10.6, 35.0), (10.6, 28.4)), ('VBAT_SENSE', 'F.Cu', 0.25, (10.6, 28.4), (12.0, 28.4)), ('VBAT_SENSE', 'F.Cu', 0.25, (12.0, 28.4), (12.6, 27.8)), ('VBAT_SENSE', 'F.Cu', 0.25, (12.6, 27.8), (16.6, 27.8)), ('VBAT_SENSE', 'F.Cu', 0.25, (16.6, 27.8), (16.8, 27.6)), ('VBAT_SENSE', 'B.Cu', 0.25, (16.8, 27.6), (18.8, 27.6)), ('VBAT_SENSE', 'F.Cu', 0.25, (18.8, 27.6), (19.0, 27.8)), ('VBAT_SENSE', 'F.Cu', 0.25, (19.0, 27.8), (26.4, 27.8)), ('VBAT_SENSE', 'B.Cu', 0.25, (26.4, 27.8), (27.8, 27.8)), ('VBAT_SENSE', 'B.Cu', 0.25, (27.8, 27.8), (28.2, 27.4)), ('VBAT_SENSE', 'F.Cu', 0.25, (28.2, 27.4), (33.8, 33.0)), ('VBAT_SENSE', 'F.Cu', 0.25, (33.8, 33.0), (33.8, 34.2)), ('VBAT_SENSE', 'F.Cu', 0.25, (33.8, 34.2), (36.2, 34.2)), ('VBAT_SENSE', 'F.Cu', 0.25, (36.2, 34.2), (37.0, 33.4)), ('VBAT_SENSE', 'F.Cu', 0.25, (37.0, 33.4), (37.0, 33.0)), ('VBAT_SENSE', 'F.Cu', 0.25, (37.0, 33.0), (40.0, 33.0)), ('VBAT_SENSE', 'F.Cu', 0.25, (40.0, 33.0), (40.8, 32.2)), ('VBAT_SENSE', 'F.Cu', 0.25, (40.8, 32.2), (40.8, 31.8)), ('VBAT_SENSE', 'F.Cu', 0.25, (40.8, 31.8), (43.2, 31.8)), ('VBAT_SENSE', 'F.Cu', 0.25, (43.2, 31.8), (44.4, 33.0)), ('VBAT_SENSE', 'F.Cu', 0.25, (44.4, 33.0), (45.0, 33.0)), ('VBUS_SENSE', 'F.Cu', 0.25, (31.8, 42.4), (31.8, 42.2)), ('VBUS_SENSE', 'B.Cu', 0.25, (31.8, 42.2), (31.8, 39.6)), ('VBUS_SENSE', 'F.Cu', 0.25, (31.8, 39.6), (31.8, 37.6)), ('VBUS_SENSE', 'B.Cu', 0.25, (31.8, 37.6), (31.8, 35.6)), ('VBUS_SENSE', 'F.Cu', 0.25, (31.8, 35.6), (29.2, 33.0)), ('VBUS_SENSE', 'F.Cu', 0.25, (29.2, 33.0), (29.2, 29.6)), ('VBUS_SENSE', 'B.Cu', 0.25, (29.2, 29.6), (30.4, 28.4)), ('VBUS_SENSE', 'F.Cu', 0.25, (30.4, 28.4), (29.0, 27.0)), ('VBUS_SENSE', 'F.Cu', 0.25, (29.0, 27.0), (29.0, 26.8)), ('VBUS_SENSE', 'F.Cu', 0.25, (29.0, 26.8), (27.8, 25.6)), ('VBUS_SENSE', 'F.Cu', 0.25, (27.8, 25.6), (27.8, 22.2)), ('VBUS_SENSE', 'F.Cu', 0.25, (27.8, 22.2), (27.0, 21.4)), ('VBUS_SENSE', 'F.Cu', 0.25, (27.0, 21.4), (27.0, 21.2)), ('VBUS_SENSE', 'B.Cu', 0.25, (27.0, 21.2), (25.8, 22.4)), ('VBUS_SENSE', 'F.Cu', 0.25, (25.8, 22.4), (25.4, 22.8)), ('VBUS_SENSE', 'F.Cu', 0.25, (25.4, 22.8), (24.8, 22.8)), ('VBUS_SENSE', 'F.Cu', 0.25, (24.8, 22.8), (24.0, 23.6)), ('VBUS_SENSE', 'F.Cu', 0.25, (24.0, 23.6), (24.0, 24.0)), ('VBUS_SENSE', 'F.Cu', 0.25, (24.0, 24.0), (21.0, 24.0)), ('GND', 'F.Cu', 0.4, (50.2, 40.8), (50.0, 40.6)), ('GND', 'F.Cu', 0.4, (50.25, 40.9), (50.2, 40.9)), ('GND', 'F.Cu', 0.4, (50.2, 40.9), (50.2, 40.8)), ('GND', 'F.Cu', 0.4, (21.0, 14.0), (20.8, 13.8)), ('GND', 'F.Cu', 0.4, (21.0, 16.4), (20.8, 16.2)), ('GND', 'F.Cu', 0.4, (21.0, 16.5), (21.0, 16.4)), ('GND', 'F.Cu', 0.4, (32.0, 9.0), (31.8, 8.8)), ('GND', 'F.Cu', 0.4, (32.0, 9.0375), (32.0, 9.0)), ('GND', 'F.Cu', 0.4, (36.0, 9.0), (35.8, 8.8)), ('GND', 'F.Cu', 0.4, (36.0, 9.0375), (36.0, 9.0)), ('GND', 'F.Cu', 0.4, (41.0, 15.0), (40.8, 14.8)), ('GND', 'F.Cu', 0.4, (52.0, 15.0), (51.8, 14.8)), ('GND', 'F.Cu', 0.4, (52.0, 15.0375), (52.0, 15.0)), ('GND', 'F.Cu', 0.4, (56.0, 15.0), (55.8, 14.8)), ('GND', 'F.Cu', 0.4, (56.0, 15.0375), (56.0, 15.0)), ('GND', 'F.Cu', 0.4, (69.6, 14.0), (69.4, 13.8)), ('GND', 'F.Cu', 0.4, (69.65, 14.0), (69.6, 14.0)), ('GND', 'F.Cu', 0.4, (79.0, 27.0), (78.8, 26.8)), ('GND', 'F.Cu', 0.4, (20.6, 36.0), (19.2, 36.0)), ('GND', 'F.Cu', 0.4, (19.2, 36.0), (19.2, 36.2)), ('GND', 'F.Cu', 0.4, (19.2, 36.2), (19.0, 36.4)), ('GND', 'F.Cu', 0.4, (20.65, 36.0), (20.6, 36.0)), ('GND', 'F.Cu', 0.4, (26.0, 24.0), (25.8, 23.8)), ('GND', 'F.Cu', 0.4, (42.0, 33.0), (41.8, 32.8)), ('GND', 'F.Cu', 0.4, (47.0, 33.0), (46.8, 32.8)), ('GND', 'F.Cu', 0.4, (47.0375, 33.0), (47.0, 33.0)), ('GND', 'F.Cu', 0.4, (9.0, 40.0), (8.8, 39.8)), ('GND', 'F.Cu', 0.4, (8.975, 40.0), (9.0, 40.0)), ('GND', 'F.Cu', 0.4, (28.0, 42.0), (27.8, 41.8)), ('GND', 'F.Cu', 0.4, (28.0, 41.9625), (28.0, 42.0)), ('GND', 'F.Cu', 0.4, (79.6, 51.6), (79.4, 51.4)), ('GND', 'F.Cu', 0.4, (79.5, 51.5375), (79.6, 51.5375)), ('GND', 'F.Cu', 0.4, (79.6, 51.5375), (79.6, 51.6)), ('GND', 'F.Cu', 0.4, (79.6, 56.0), (79.4, 55.8)), ('GND', 'F.Cu', 0.4, (79.5, 56.0375), (79.6, 56.0375)), ('GND', 'F.Cu', 0.4, (79.6, 56.0375), (79.6, 56.0)), ('GND', 'F.Cu', 0.4, (71.0, 57.6), (70.8, 57.4)), ('GND', 'F.Cu', 0.4, (71.0375, 57.5), (71.0, 57.5)), ('GND', 'F.Cu', 0.4, (71.0, 57.5), (71.0, 57.6)), ('GND', 'F.Cu', 0.4, (62.0, 40.4), (61.8, 40.2)), ('GND', 'F.Cu', 0.4, (62.0375, 40.5), (62.0, 40.5)), ('GND', 'F.Cu', 0.4, (62.0, 40.5), (62.0, 40.4)), ('GND', 'F.Cu', 0.4, (61.0, 50.6), (60.8, 50.4)), ('GND', 'F.Cu', 0.4, (61.0, 50.5625), (61.0, 50.6)), ('GND', 'F.Cu', 0.4, (53.0, 50.6), (52.8, 50.4)), ('GND', 'F.Cu', 0.4, (53.0, 50.5625), (53.0, 50.6)), ('GND', 'F.Cu', 0.4, (36.0, 12.4), (35.8, 12.2)), ('GND', 'F.Cu', 0.4, (36.0, 12.5), (36.0, 12.4)), ('GND', 'F.Cu', 0.4, (24.0, 46.0), (23.8, 45.8)), ('GND', 'F.Cu', 0.4, (8.0, 46.0), (7.8, 45.8))]
VIAS = [('GND', 21.0, 20.0, 0.8, 0.4), ('GND', 41.0, 10.0, 0.8, 0.4), ('GND', 71.6, 51.6, 0.8, 0.4), ('+3V3_MCU', 29.8, 35.0, 0.8, 0.4), ('+3V3_MCU', 28.6, 36.2, 0.8, 0.4), ('USB_DM', 30.6, 45.6, 0.8, 0.4), ('USB_DM', 29.2, 47.0, 0.8, 0.4), ('USB_DM', 18.0, 19.2, 0.8, 0.4), ('USB_DM', 19.2, 18.0, 0.8, 0.4), ('USB_DP_CON', 17.0, 20.2, 0.8, 0.4), ('USB_DP_CON', 19.0, 20.2, 0.8, 0.4), ('USB_CC1', 14.8, 17.6, 0.8, 0.4), ('USB_CC1', 17.2, 15.2, 0.8, 0.4), ('USB_CC2', 16.0, 18.8, 0.8, 0.4), ('USB_CC2', 18.4, 16.4, 0.8, 0.4), ('MOSI_MCU', 57.4, 48.4, 0.8, 0.4), ('MOSI_MCU', 59.4, 48.4, 0.8, 0.4), ('OLED_DC_MCU', 57.4, 45.4, 0.8, 0.4), ('OLED_DC_MCU', 59.4, 45.4, 0.8, 0.4), ('OLED_CS_MCU', 57.0, 42.4, 0.8, 0.4), ('OLED_CS_MCU', 58.4, 41.0, 0.8, 0.4), ('SCLK', 57.4, 51.6, 0.8, 0.4), ('SCLK', 57.4, 53.6, 0.8, 0.4), ('SCLK', 65.0, 54.8, 0.8, 0.4), ('SCLK', 68.0, 54.8, 0.8, 0.4), ('SCLK', 72.2, 49.4, 0.8, 0.4), ('SCLK', 74.2, 49.4, 0.8, 0.4), ('MOSI', 67.6, 43.6, 0.8, 0.4), ('MOSI', 67.6, 42.0, 0.8, 0.4), ('MOSI', 72.2, 42.4, 0.8, 0.4), ('MOSI', 74.2, 42.4, 0.8, 0.4), ('OLED_RES', 56.6, 46.2, 0.8, 0.4), ('OLED_RES', 60.4, 42.0, 0.8, 0.4), ('OLED_RES', 72.2, 41.2, 0.8, 0.4), ('OLED_RES', 74.2, 41.2, 0.8, 0.4), ('OLED_DC', 63.4, 43.6, 0.8, 0.4), ('OLED_DC', 63.4, 40.4, 0.8, 0.4), ('OLED_DC', 72.2, 40.0, 0.8, 0.4), ('OLED_DC', 74.2, 40.0, 0.8, 0.4), ('OLED_CS', 56.6, 43.4, 0.8, 0.4), ('OLED_CS', 58.4, 39.8, 0.8, 0.4), ('OLED_CS', 72.2, 38.4, 0.8, 0.4), ('OLED_CS', 74.2, 38.4, 0.8, 0.4), ('E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
