Soulboy420/BP_flappyBird/hardware/gen/labels.py

# -*- coding: utf-8 -*-
"""Automatisch erzeugt von mk_labels.py."""
LABEL_OFF = {'D1': (0.0, -3.1), 'D2': (0.0, -2.0), 'D3': (2.48, -2.48), 'D4': (-4.6, 0.0), 'D5': (0.0, -2.5), 'J1': (0.0, -2.5), 'J2': (-3.04, -3.04), 'J3': (4.6, 0.0), 'J4': (0.0, -3.8), 'J5': (0.0, -3.8), 'SW1': (-3.04, 3.04), 'U1': (1.6, 0.0), 'U2': (-5.6, 0.0), 'U3': (0.0, -3.8), 'C1': (2.0, 0.0), 'C10': (-4.48, -4.48), 'C11': (-2.5, 0.0), 'C12': (0.0, 4.6), 'C2': (0.0, -2.5), 'C3': (-2.0, 0.0), 'C4': (-2.0, 0.0), 'C5': (1.6, -1.6), 'C6': (0.0, -5.6), 'C7': (0.0, 3.1), 'C8': (2.0, 0.0), 'C9': (2.0, 0.0), 'F1': (-1.6, 1.6), 'H1': (0.0, -2.0), 'H2': (0.0, -2.0), 'H3': (2.5, 0.0), 'H4': (0.0, 2.0), 'R1': (-3.1, 0.0), 'R10': (2.48, 2.48), 'R11': (0.0, 3.8), 'R12': (0.0, 3.8), 'R13': (-1.6, 1.6), 'R14': (2.48, 2.48), 'R15': (4.6, 0.0), 'R16': (1.6, 1.6), 'R17': (0.0, -1.6), 'R18': (3.04, -3.04), 'R19': (0.0, -1.6), 'R2': (0.0, 1.6), 'R20': (0.0, 1.6), 'R21': (0.0, 1.6), 'R22': (0.0, 4.6), 'R23': (0.0, 4.6), 'R3': (-2.48, -2.48), 'R4': (4.48, -4.48), 'R5': (0.0, 3.1), 'R6': (-2.0, 2.0), 'R7': (3.8, 0.0), 'R8': (0.0, -1.6), 'R9': (-4.48, -4.48), 'TP1': (2.0, -2.0), 'TP10': (-2.0, 2.0), 'TP11': (-3.04, 3.04), 'TP12': (3.1, 0.0), 'TP2': (0.0, -2.0), 'TP3': (-3.04, -3.04), 'TP4': (-2.5, 0.0), 'TP5': (0.0, -2.0), 'TP6': (0.0, -4.6), 'TP7': (0.0, -2.5)}
